Pybarguen/Rpm_Reader_PIC18F26J50/Pcb_Files/RPM_Meter_Circuit.kicad_sch

## KiCad design Pcb_Files/RPM_Meter_Circuit.kicad_sch (2024-12-31, an earlier design)

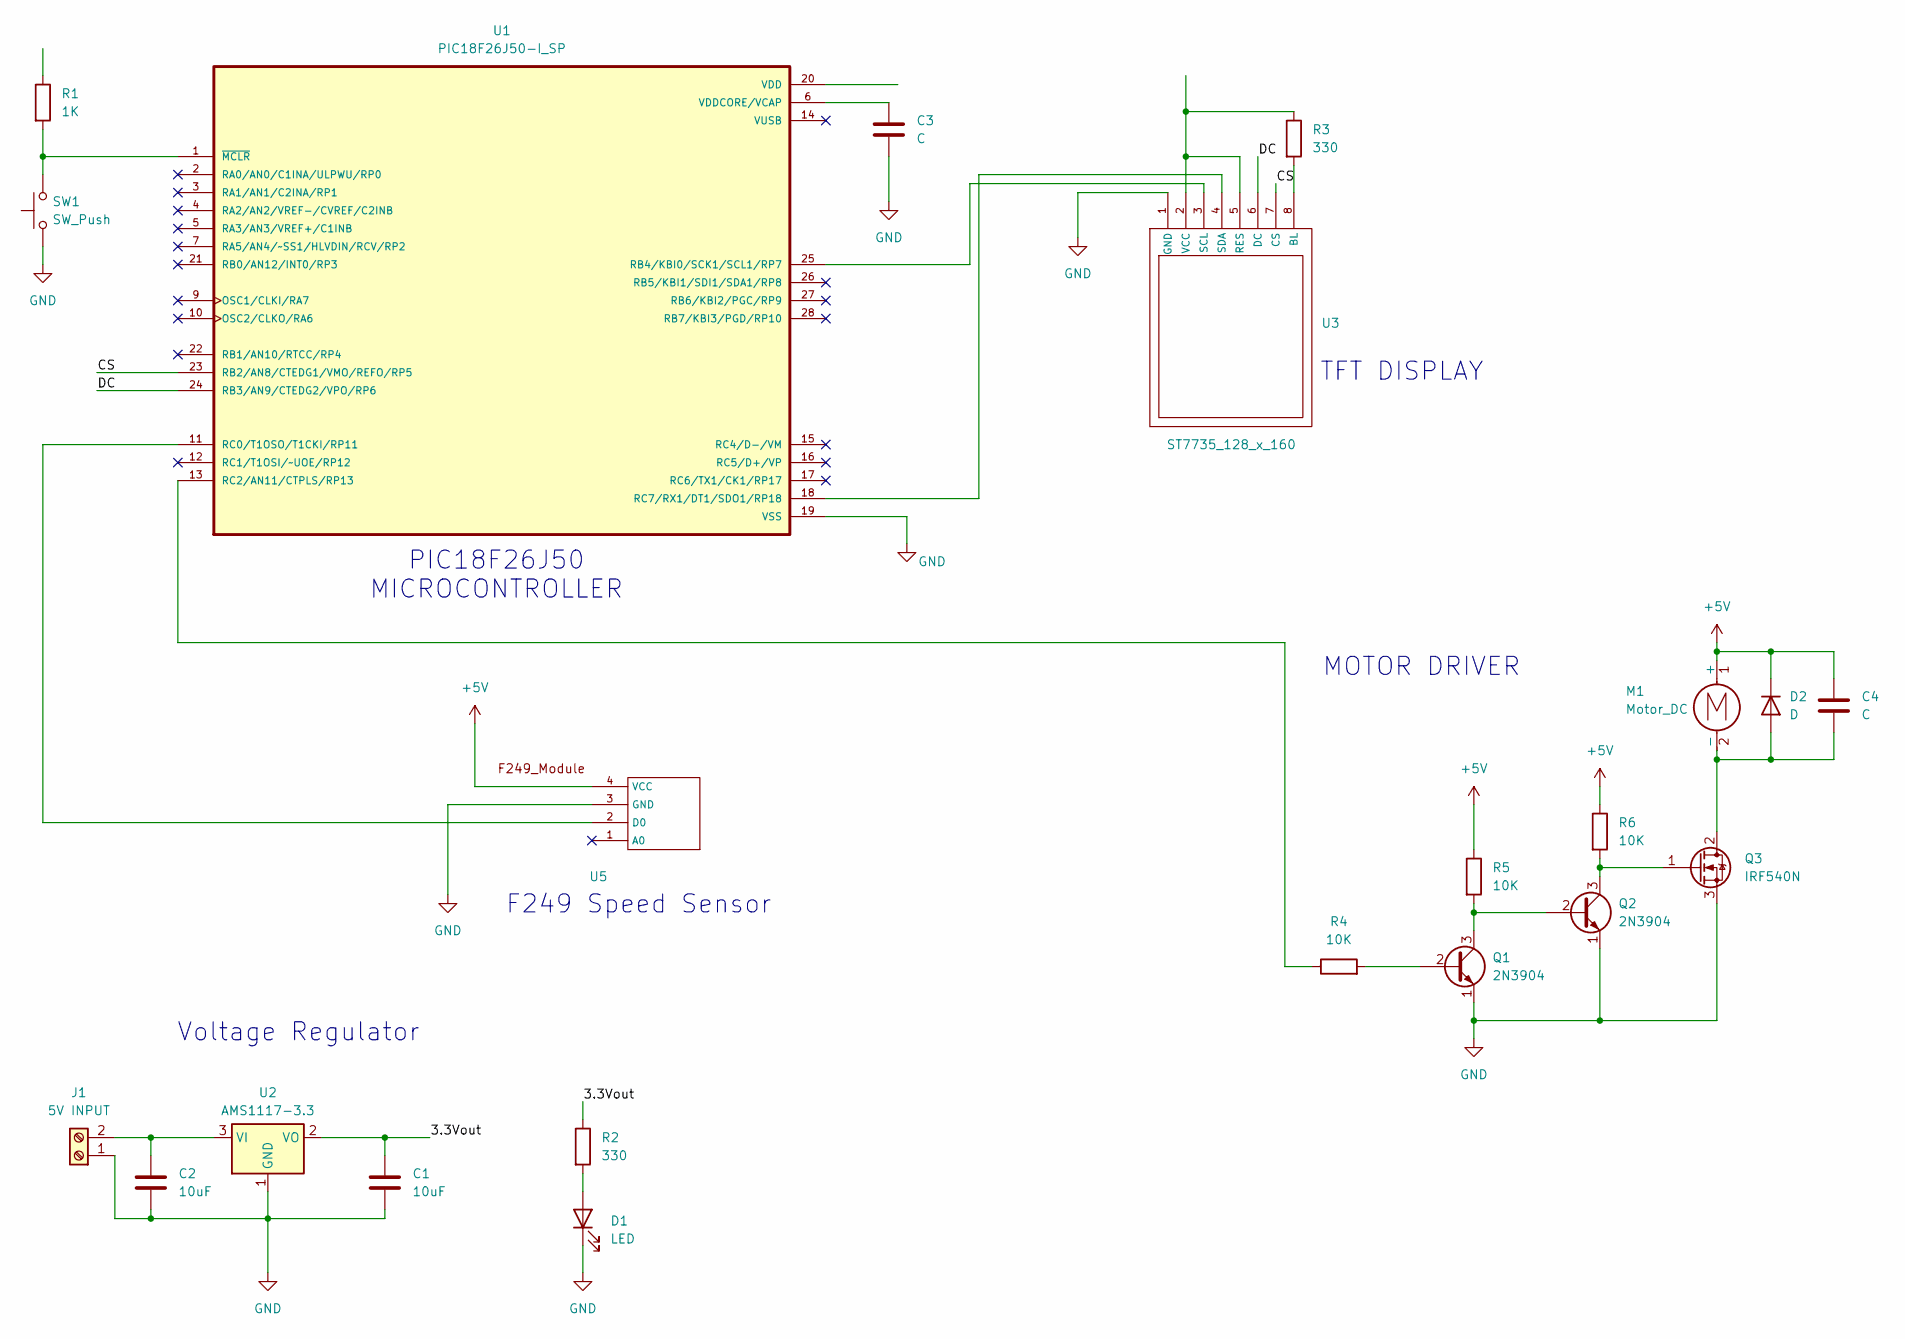
[picture p2: schematic RPM_Meter_Circuit.kicad_sch]

Parts:
C1, C2: 10uF
C3, C4: C
D1: LED
D2: D
J1: 5V INPUT
M1: Motor_DC
Q1, Q2: 2N3904; TO-92_Inline
Q3: IRF540N; TO-220-3_Vertical
R1: 1K
R2, R3: 330
R4, R5, R6: 10K
SW1: SW_Push
U1: PIC18F26J50-I_SP; DIP787W46P254L3467H508Q28
U2: AMS1117-3.3; SOT-223-3_TabPin2
U3: ST7735_128_x_160
U5: (no value)

Connections:
3.3Vout: C1.1, R2.1, U2.2 (VO)
+5V: C4.1, D2.1 (K), M1.1 (+), R5.1, R6.1, U5.4 (VCC)
CS: U1.23 (RB2/AN8/CTEDG1/VMO/REFO/RP5), U3.7 (CS)
DC: U1.24 (RB3/AN9/CTEDG2/VPO/RP6), U3.6 (DC)
GND: C1.2, C2.2, C3.2, D1.1 (K), J1.1, Q1.1 (E), Q2.1 (E), Q3.3 (S), SW1.1, U1.19 (VSS), U2.1 (GND), U3.1 (GND), U5.3 (GND)
unnamed: C2.1, J1.2, U2.3 (VI)
unnamed: C3.1, U1.6 (VDDCORE/VCAP)
unnamed: C4.2, D2.2 (A), M1.2 (-), Q3.2 (D)
unnamed: D1.2 (A), R2.2
unnamed: Q1.2 (B), R4.2
unnamed: Q1.3 (C), Q2.2 (B), R5.2
unnamed: Q2.3 (C), Q3.1 (G), R6.2
unnamed: R1.2, SW1.2, U1.1 (~MCLR)
unnamed: R3.1, U3.2 (VCC), U3.5 (RES)
unnamed: R3.2, U3.8 (BL)
unnamed: R4.1, U1.13 (RC2/AN11/CTPLS/RP13)
unnamed: U1.11 (RC0/T1OSO/T1CKI/RP11), U5.2 (D0)
unnamed: U1.18 (RC7/RX1/DT1/SDO1/RP18), U3.4 (SDA)
unnamed: U1.25 (RB4/KBI0/SCK1/SCL1/RP7), U3.3 (SCL)

Notes on the sheet:
Voltage Regulator
F249 Speed Sensor
TFT DISPLAY
PIC18F26J50 MICROCONTROLLER
MOTOR DRIVER
